Elektropioneer/AX_Arduino_CAN/Hardware/Output/Images/bottom_view.png

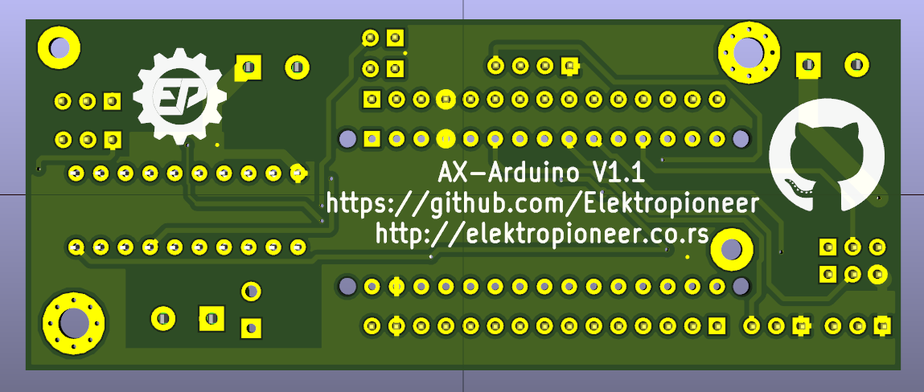
Hardware/Output/Images/bottom_view.png
