Elektropioneer/AX_Arduino_CAN/Hardware/Output/Images/top_view.png

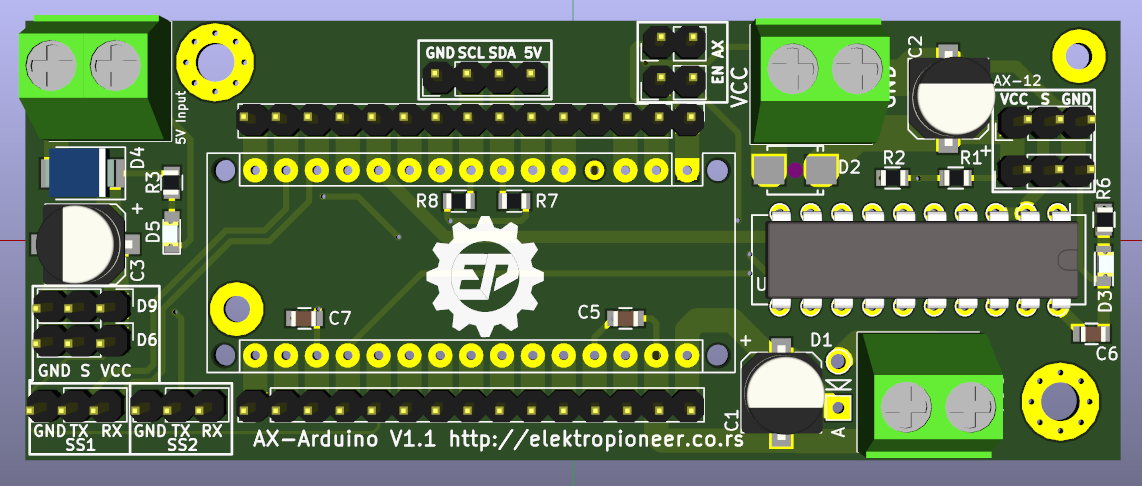
Hardware/Output/Images/top_view.png
